tokyohost/pico-vision/monitor/assert/fishQr.png

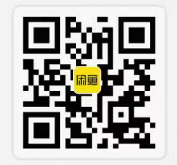
monitor/assert/fishQr.png
