tokyohost/pico-vision/monitor/assert/qqgroup.png

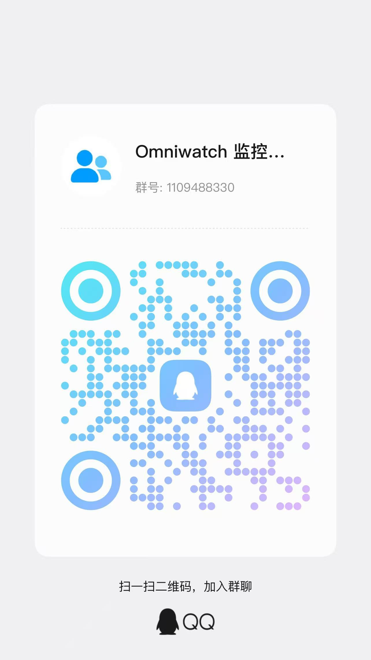
monitor/assert/qqgroup.png
