tokyohost/pico-vision/monitor/win/ui-web/assert/style/disk.png

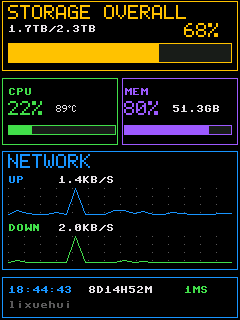
monitor/win/ui-web/assert/style/disk.png
