tokyohost/pico-vision/monitor/win/ui-web/assert/style/diskv2.png

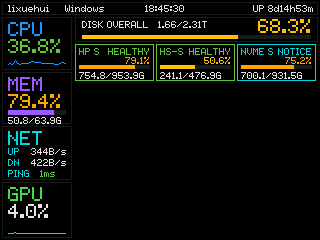
monitor/win/ui-web/assert/style/diskv2.png
