tokyohost/pico-vision/monitor/win/ui-web/assert/style/fps_simple.png

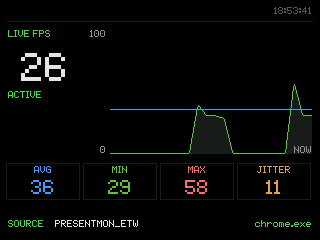
monitor/win/ui-web/assert/style/fps_simple.png
