tokyohost/pico-vision/monitor/win/ui-web/assert/style/game.png

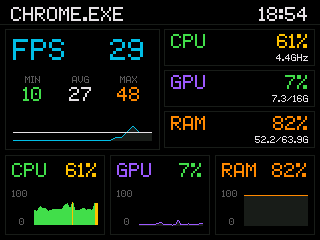
monitor/win/ui-web/assert/style/game.png
