tokyohost/pico-vision/monitor/win/ui-web/assert/style/horizontal_disk4x_qb.png

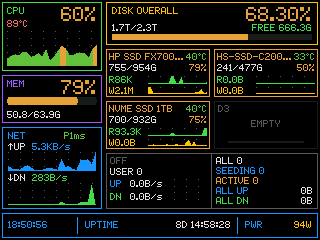
monitor/win/ui-web/assert/style/horizontal_disk4x_qb.png
