tokyohost/pico-vision/monitor/win/ui-web/assert/style/horizontal_disk.png

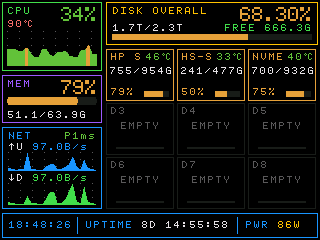
monitor/win/ui-web/assert/style/horizontal_disk.png
