tokyohost/pico-vision/monitor/win/ui-web/assert/style/horizontal_diskv2.png

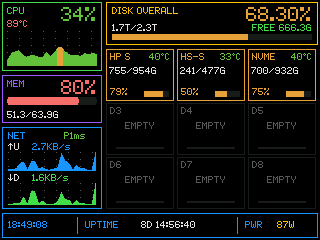
monitor/win/ui-web/assert/style/horizontal_diskv2.png
