tokyohost/pico-vision/monitor/win/ui-web/assert/style/simple.png

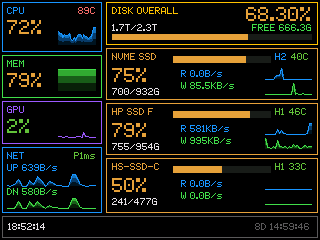
monitor/win/ui-web/assert/style/simple.png
