tokyohost/pico-vision/monitor/win/ui-web/assert/style/thermal_watch.png

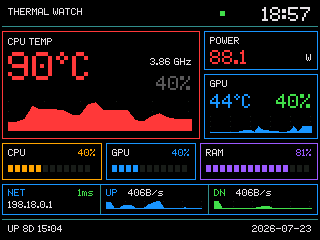
monitor/win/ui-web/assert/style/thermal_watch.png
