tokyohost/pico-vision/pcb/LED_MOSFET_PWM_V4_JLC_FREE_完整资料包/led_mosfet_pwm_board_v4_jlc_free/pcb_preview_v4_jlc_free.png

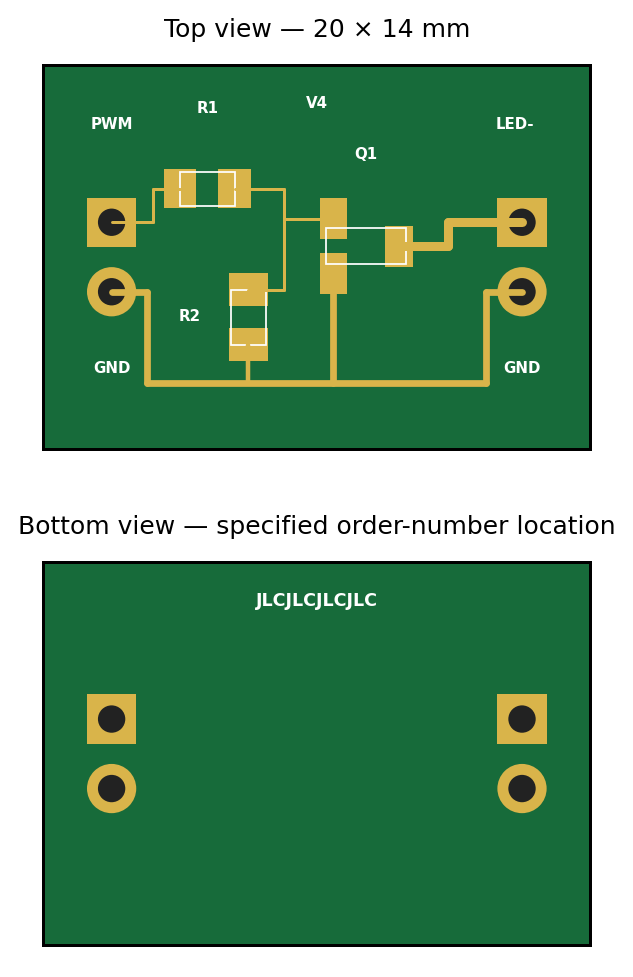
pcb/LED_MOSFET_PWM_V4_JLC_FREE_完整资料包/led_mosfet_pwm_board_v4_jlc_free/pcb_preview_v4_jlc_free.png
