tokyohost/pico-vision/pcb/v12/build/03_Docs/dimensions.png

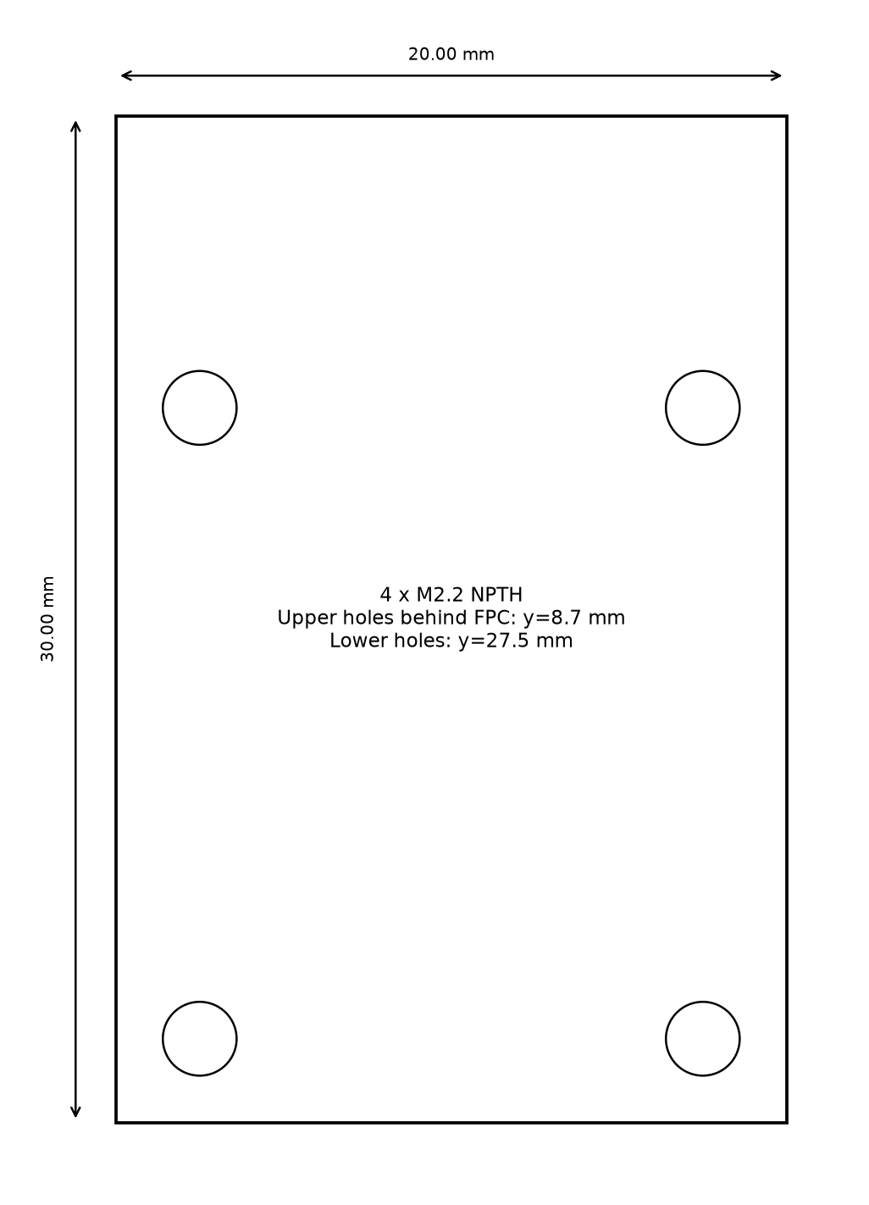
pcb/v12/build/03_Docs/dimensions.png
