tokyohost/pico-vision/pcb/v12/build/03_Docs/gerber_orientation_check.png

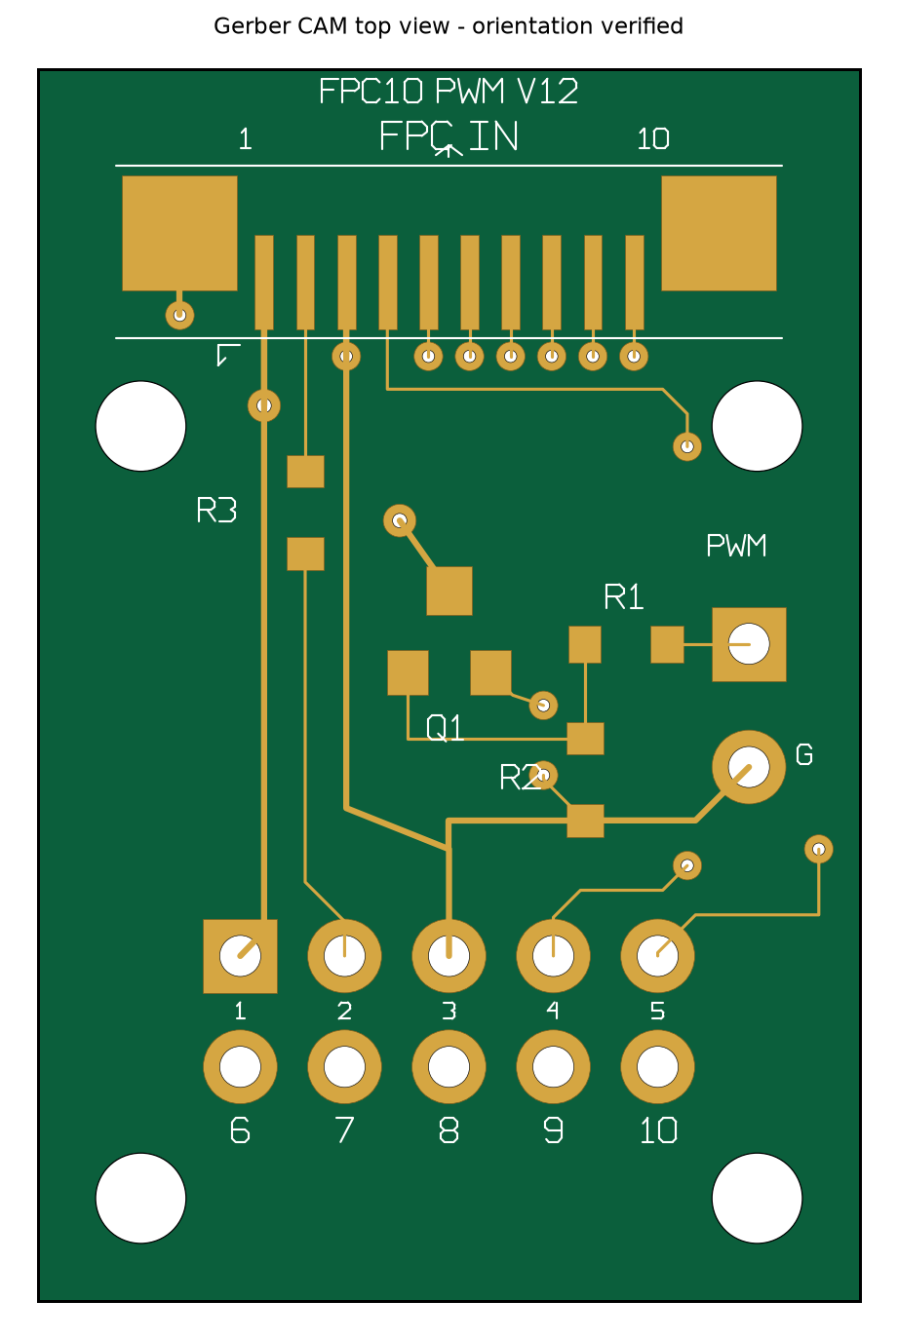
pcb/v12/build/03_Docs/gerber_orientation_check.png
