tokyohost/pico-vision/pcb/v12/build/03_Docs/preview_bottom.png

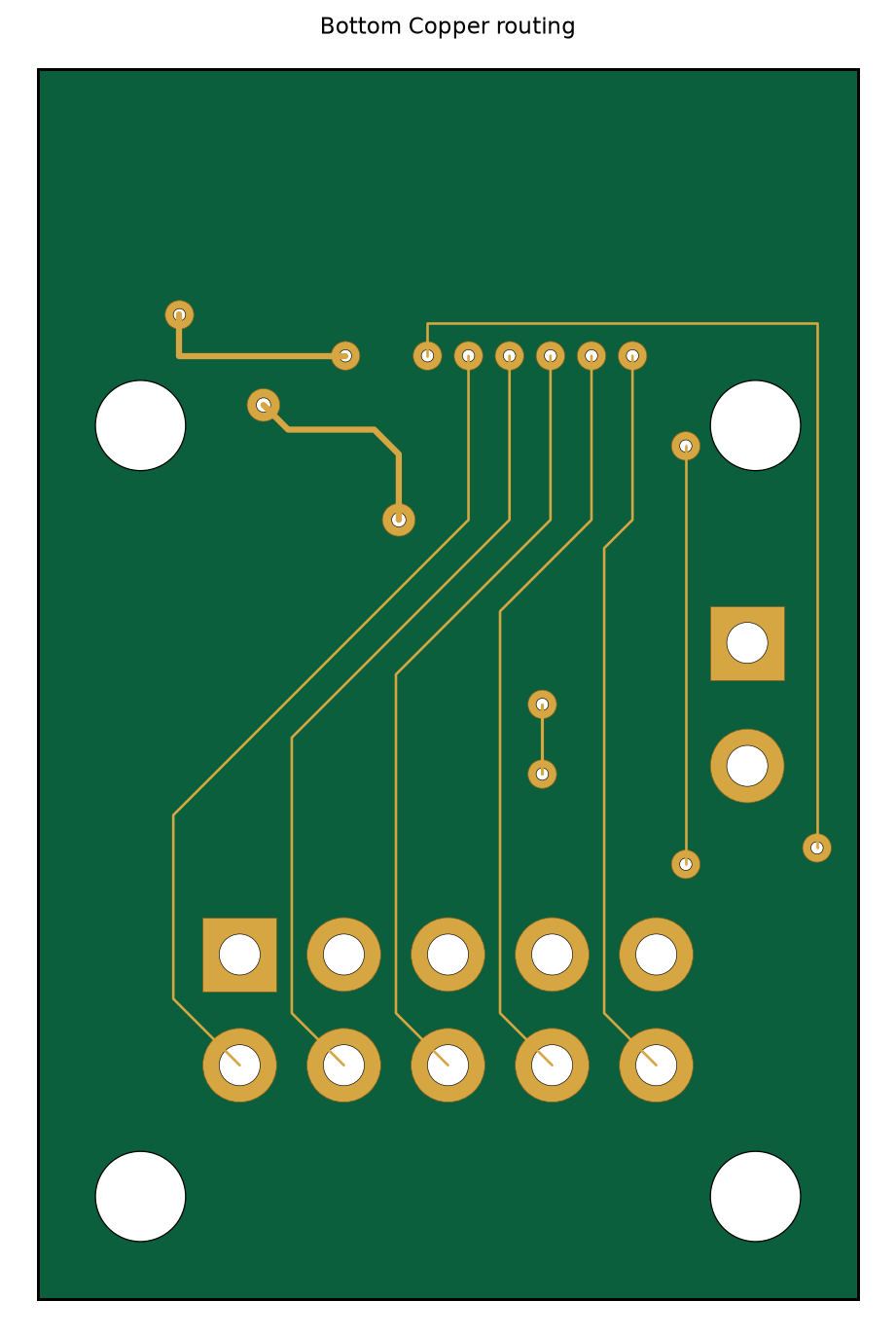
pcb/v12/build/03_Docs/preview_bottom.png
