tokyohost/pico-vision/monitor/custom_data_runner.py

#!/usr/bin/env python3
"""在隔离子进程中加载自定义数据插件并输出协议 JSON。"""

import importlib.util
import contextlib
import json
import sys
import traceback
from pathlib import Path


def _load_module(script_path):
    """从指定入口文件加载插件模块。"""
    plugin_directory = str(Path(script_path).resolve().parent)
    if plugin_directory not in sys.path:
        sys.path.insert(0, plugin_directory)
    specification = importlib.util.spec_from_file_location("omniwatch_custom_data_plugin", script_path)
    if specification is None or specification.loader is None:
        raise RuntimeError("无法加载插件入口模块")
    module = importlib.util.module_from_spec(specification)
    specification.loader.exec_module(module)
    return module


def _load_collect(script_path):
    """加载插件并返回经过校验的 collect 方法。"""
    with contextlib.redirect_stdout(sys.stderr):
        module = _load_module(script_path)
        collect = getattr(module, "collect", None)
        if not callable(collect):
            raise RuntimeError("插件入口必须定义 collect() 方法")
    return collect


def _collect(collect, config_json):
    """执行已加载的 collect 方法并校验返回值可序列化。"""
    with contextlib.redirect_stdout(sys.stderr):
        parameters = __import__("inspect").signature(collect).parameters
        result = collect() if not parameters else collect(config_json)
    json.dumps(result, ensure_ascii=False)
    return result


def main():
    """执行插件并仅向标准输出写入一条协议 JSON。"""
    if len(sys.argv) != 2:
        print(json.dumps({"ok": False, "error": "缺少插件入口路径"}, ensure_ascii=False))
        return 2
    try:
        collect = _load_collect(Path(sys.argv[1]).resolve())
    except Exception:
        print(json.dumps({"ok": False, "error": traceback.format_exc()}, ensure_ascii=False), flush=True)
        return 1
    for line in sys.stdin:
        try:
            request = json.loads(line)
            if request.get("command") == "stop":
                return 0
            if request.get("command") != "collect":
                raise RuntimeError("不支持的插件进程命令")
            response = {"ok": True, "data": _collect(collect, request.get("config", "{}"))}
        except Exception:
            response = {"ok": False, "error": traceback.format_exc()}
        print(json.dumps(response, ensure_ascii=False), flush=True)
    return 0


if __name__ == "__main__":
    raise SystemExit(main())
