tokyohost/pico-vision/monitor/monitor_core/style_commands.py

"""Pico 样式、截图与热配置命令处理。"""

import json
import logging
import os
import queue
from datetime import datetime
from pathlib import Path

import serial

from .console import configure_logging
from .ui_helpers import normalize_style_catalog

LOGGER = logging.getLogger("pico-monitor")
BUILTIN_LCD_STYLES = (
    "default", "disk", "diskv2", "diskv3", "diskv4", "horizontal_disk",
    "horizontal_diskv2", "horizontal_disk4x", "horizontal_disk4x_qb",
    "horizontal_disk6x", "simple", "fpstest", "fps_simple", "game",
    "idle",
)


class StyleCommandMixin:
    """提供样式管理、截图和运行时显示配置能力。"""

    def _synchronize_style_catalog(self):
        """接收 Pico 样式清单并更新 monitor 的 JSON 配置文件。"""
        catalog = getattr(self.client, "styles", None)
        if catalog is None:
            return
        catalog = catalog if isinstance(catalog, (list, tuple)) else []
        names = set(BUILTIN_LCD_STYLES)
        names.update({
            item.get("name") for item in catalog
            if isinstance(item, dict) and item.get("name")
        })
        if not names:
            return
        self.available_styles = names
        self.available_idle_styles = {
            item.get("name") for item in catalog
            if isinstance(item, dict) and item.get("name") and item.get("idle") is True
        } or {"idle"}
        settings_path = os.getenv("PICO_MONITOR_SETTINGS_PATH")
        if settings_path:
            from win.settings import TraySettingsStore

            normalized = normalize_style_catalog(catalog)
            if normalized:
                store = TraySettingsStore(settings_path)
                settings = store.load()
                settings["styles"] = normalized
                if settings["lcd_style"] not in names:
                    settings["lcd_style"] = normalized[0]["name"]
                    self.arguments.lcd_style = settings["lcd_style"]
                if settings["idle_style"] not in self.available_idle_styles:
                    settings["idle_style"] = "idle"
                    self.arguments.idle_style = settings["idle_style"]
                store.save(settings)
        LOGGER.info("STYLE_CATALOG_UPDATED：已同步 %d 个 Pico 样式", len(names))

    def request_reboot_and_stop(self):
        """让主循环退出，并在释放串口前请求 Pico 重启。"""
        LOGGER.info("收到托盘退出请求，将在停止监控前重启 Pico")
        self.reboot_requested.set()
        self.stopping.set()

    def request_sdk_bootloader_and_stop(self):
        """让主循环退出，并在释放 USB 前请求设备进入 ROM 下载模式。"""
        LOGGER.info("收到托盘 SDK 刷写请求，将在停止监控前切换 ROM USB 模式")
        self.sdk_bootloader_requested.set()
        self.stopping.set()

    def request_custom_style_catalog(self, result_queue=None):
        """安排主循环在当前串口交互结束后查询自定义样式。"""
        waiters = getattr(self, "custom_style_catalog_waiters", None)
        if result_queue is not None and waiters is not None:
            waiters.put(result_queue)
        self.custom_style_catalog_requested.set()

    def request_screenshot(self, result_queue=None):
        """安排主循环在当前串口交互完成后截取 LCD 画面。"""
        waiters = getattr(self, "screenshot_waiters", None)
        if result_queue is not None and waiters is not None:
            waiters.put(result_queue)
        self.screenshot_requested.set()

    def _publish_screenshot(self):
        """接收 Pico 截图、转换为 PNG，并把保存结果输出给托盘。"""
        self.screenshot_requested.clear()
        try:
            from PIL import Image

            metadata, pixels = self.client.screenshot()
            width = int(metadata["width"])
            height = int(metadata["height"])
            # Pillow 的 BGR;16 解码器读取小端 RGB565，Pico 回传的是 LCD 使用的
            # 大端字节序，因此先按像素交换高低字节再生成 PNG。
            little_endian_pixels = bytearray(len(pixels))
            little_endian_pixels[0::2] = pixels[1::2]
            little_endian_pixels[1::2] = pixels[0::2]
            image = Image.frombytes(
                "RGB", (width, height), bytes(little_endian_pixels), "raw", "BGR;16"
            )
            screenshot_directory = Path(
                os.getenv("PICO_MONITOR_SCREENSHOT_DIR", Path.cwd() / "screenshot")
            )
            screenshot_directory.mkdir(parents=True, exist_ok=True)
            path = screenshot_directory / datetime.now().strftime(
                "screenshot_%Y%m%d_%H%M%S_%f.png"
            )
            image.save(path, "PNG")
            result = {"status": "ok", "path": str(path.resolve())}
        except (KeyError, OSError, RuntimeError, ValueError, serial.SerialException) as error:
            result = {"status": "error", "message": str(error)}
        print(
            "SCREENSHOT_RESULT:"
            + json.dumps(result, ensure_ascii=False, separators=(",", ":")),
            flush=True,
        )
        waiters = getattr(self, "screenshot_waiters", None)
        try:
            waiter = waiters.get_nowait() if waiters is not None else None
        except queue.Empty:
            waiter = None
        if waiter is not None:
            waiter.put(result)

    def _publish_custom_style_catalog(self):
        """通过 Pico 指令查询全部样式，同步配置后输出给托盘进程。"""
        self.custom_style_catalog_requested.clear()
        try:
            catalog = self.client.request_style_catalog_info()
            latest_styles = catalog["styles"]
            if not isinstance(latest_styles, list):
                raise ValueError("设备样式目录格式无效")
            self.client.styles = latest_styles
            self._synchronize_style_catalog()
            result = {
                "status": "ok",
                "styles": latest_styles,
                "flash": catalog["flash"],
                "active_style": catalog.get("active_style", ""),
            }
        except (KeyError, ValueError, OSError, RuntimeError, serial.SerialException) as error:
            result = {"status": "error", "message": str(error), "styles": []}
        print(
            "CUSTOM_STYLE_LIST_RESULT:"
            + json.dumps(result, ensure_ascii=False, separators=(",", ":")),
            flush=True,
        )
        waiters = getattr(self, "custom_style_catalog_waiters", None)
        try:
            waiter = waiters.get_nowait() if waiters is not None else None
        except queue.Empty:
            waiter = None
        if waiter is not None:
            waiter.put(result)

    def request_custom_style_upload(self, payload, result_queue=None):
        """安排主循环在串口空闲时上传一个已校验的自定义样式。"""
        waiters = getattr(self, "custom_style_upload_waiters", None)
        if result_queue is not None and waiters is not None:
            waiters.put(result_queue)
        self.custom_style_uploads.put(dict(payload))

    def _publish_custom_style_upload(self):
        """执行待处理的自定义样式上传并向托盘输出结构化结果。"""
        payload = self.custom_style_uploads.get_nowait()
        try:
            import base64

            content = base64.b64decode(payload["content"], validate=True)

            def publish_progress(progress):
                """输出样式上传进度，供管理界面实时展示已发送字节数。"""
                print(
                    "CUSTOM_STYLE_UPLOAD_PROGRESS:"
                    + json.dumps(
                        progress,
                        ensure_ascii=False,
                        separators=(",", ":"),
                    ),
                    flush=True,
                )

            data = self.client.upload_style(
                payload["filename"],
                payload["style_name"],
                content,
                overwrite=payload.get("overwrite") is True,
                progress_callback=publish_progress,
            )
            result = {"status": "ok", "data": data}
            self.client.styles = self.client.request_style_catalog()
            self._synchronize_style_catalog()
        except (KeyError, ValueError, OSError, RuntimeError, serial.SerialException) as error:
            result = {"status": "error", "message": str(error)}
        print(
            "CUSTOM_STYLE_UPLOAD_RESULT:"
            + json.dumps(result, ensure_ascii=False, separators=(",", ":")),
            flush=True,
        )
        waiters = getattr(self, "custom_style_upload_waiters", None)
        try:
            waiter = waiters.get_nowait() if waiters is not None else None
        except queue.Empty:
            waiter = None
        if waiter is not None:
            waiter.put(result)

    def request_custom_style_delete(self, payload, result_queue=None):
        """安排主循环删除指定自定义样式。"""
        waiters = getattr(self, "custom_style_delete_waiters", None)
        if result_queue is not None and waiters is not None:
            waiters.put(result_queue)
        self.custom_style_deletes.put(dict(payload))

    def _publish_custom_style_delete(self):
        """删除设备自定义样式、刷新目录并向托盘发布结果。"""
        payload = self.custom_style_deletes.get_nowait()
        try:
            data = self.client.delete_style(
                payload["filename"], payload["style_name"],
            )
            latest_styles = data.get("styles")
            if not isinstance(latest_styles, list):
                raise ValueError("设备删除响应缺少最新样式列表")
            self.client.styles = latest_styles
            self._synchronize_style_catalog()
            result = {
                "status": "ok",
                "data": data,
                "styles": latest_styles,
            }
        except (KeyError, ValueError, OSError, RuntimeError, serial.SerialException) as error:
            result = {"status": "error", "message": str(error)}
        print(
            "CUSTOM_STYLE_DELETE_RESULT:"
            + json.dumps(result, ensure_ascii=False, separators=(",", ":")),
            flush=True,
        )
        waiters = getattr(self, "custom_style_delete_waiters", None)
        try:
            waiter = waiters.get_nowait() if waiters is not None else None
        except queue.Empty:
            waiter = None
        if waiter is not None:
            waiter.put(result)

    def apply_display_config(self, payload):
        """校验并热更新 Windows 托盘下发的显示配置。"""
        brightness = int(payload.get("lcd_brightness", self.arguments.lcd_brightness))
        rotation = int(payload.get("screen_rotation", self.arguments.screen_rotation))
        style = payload.get("lcd_style", self.arguments.lcd_style)
        idle_enabled = bool(payload.get("idle_enabled", getattr(self.arguments, "idle_enabled", True)))
        idle_style = payload.get("idle_style", getattr(self.arguments, "idle_style", "idle"))
        idle_timeout = int(payload.get("idle_timeout", getattr(self.arguments, "idle_timeout", 30)))
        network_unit = payload.get("network_unit", self.arguments.network_unit)
        if not 1 <= brightness <= 100:
            raise ValueError("LCD 背光亮度必须为 1 至 100")
        if rotation not in (0, 180):
            raise ValueError("屏幕旋转角度仅支持 0 或 180")
        if style not in self.available_styles:
            raise ValueError("不支持的 LCD 样式")
        if idle_enabled and idle_style not in getattr(self, "available_idle_styles", {"idle"}):
            raise ValueError("不支持的 LCD 待机样式")
        if idle_enabled and idle_timeout <= 0:
            raise ValueError("待机秒数必须大于 0")
        if network_unit not in ("MB", "Mbps"):
            raise ValueError("不支持的网络速率单位")
        self.arguments.lcd_brightness = brightness
        self.arguments.screen_rotation = rotation
        self.arguments.lcd_style = style
        self.arguments.idle_enabled = idle_enabled
        self.arguments.idle_style = idle_style
        self.arguments.idle_timeout = idle_timeout
        self.arguments.network_unit = network_unit
        LOGGER.info(
            "显示设置已热更新：亮度=%d%%，旋转=%d°，样式=%s，允许待机=%s，待机样式=%s，待机=%d 秒，网络单位=%s",
            brightness, rotation, style, idle_enabled, idle_style, idle_timeout, network_unit,
        )

    def apply_dev_config(self, payload):
        """热更新开发模式开关，不重启 Monitor 工作进程。"""
        enabled = payload.get("enabled")
        if not isinstance(enabled, bool):
            raise ValueError("开发模式开关必须为布尔值")
        self.arguments.dev = enabled
        configure_logging("DEBUG" if enabled else self.arguments.log_level)
        LOGGER.info("开发模式已热更新：%s", "开启" if enabled else "关闭")

    def stop(self, signum=None, frame=None):
        """请求主循环停止，由通信线程在退出阶段统一关闭串口。"""
        del signum, frame
        LOGGER.info("收到停止请求，正在关闭监控程序")
        # Windows 的 PySerial 正在 ReadFile 时不能由其他线程执行 close，
        # 否则内部 OVERLAPPED 事件会被置空并触发 ctypes.byref(None) 异常。
        self.stopping.set()
