tokyohost/pico-vision/monitor/sdk_flash.py

"""校验 ESP32-S3 SDK 镜像并通过 esptool 执行受控 USB 刷写。"""

import argparse
import hashlib
import json
import re
import struct
import sys
import time
from contextlib import redirect_stdout
from dataclasses import dataclass
from pathlib import Path

from serial.tools import list_ports


ESP32_IMAGE_MAGIC = 0xE9
ESP32_S3_IMAGE_CHIP_ID = 9
ESP32_S3_PARTITION_TABLE_OFFSET = 0x8000
ESP32_S3_APPLICATION_OFFSET = 0x10000
ESPRESSIF_USB_VENDOR_ID = 0x303A
PARTITION_ENTRY_MAGIC = 0x50AA
PARTITION_ENTRY_SIZE = 32
MAXIMUM_SDK_IMAGE_SIZE = 8 * 1024 * 1024
SDK_VERSION_PATTERN = re.compile(
    rb"MPY version\s*:\s*(v[^\x00\r\n]{1,80}?)\s+on\s+\d{4}-\d{2}-\d{2}"
)


@dataclass(frozen=True)
class SdkPartition:
    """保存 SDK 合并镜像中的一个 ESP32 分区表项。"""

    partition_type: int
    subtype: int
    offset: int
    size: int
    label: str


@dataclass(frozen=True)
class SdkImageInformation:
    """保存通过全部安全校验的 SDK 镜像摘要。"""

    path: Path
    size: int
    sha256: str
    sdk_version: str
    partitions: tuple


class _ForwardingTextRecorder:
    """实时转发 esptool 标准输出，并保留用于判断收尾状态的文本。"""

    def __init__(self, target):
        """保存输出目标并初始化本次刷写的文本片段。"""
        self._target = target
        self._parts = []

    def write(self, content):
        """记录并立即转发一段文本，保持界面刷写日志实时更新。"""
        text = str(content)
        self._parts.append(text)
        return self._target.write(text)

    def flush(self):
        """立即刷新真实输出目标。"""
        return self._target.flush()

    def isatty(self):
        """返回真实输出目标的终端能力。"""
        method = getattr(self._target, "isatty", None)
        return bool(method()) if method is not None else False

    def getvalue(self):
        """合并并返回已经记录的全部输出。"""
        return "".join(self._parts)

    def __getattr__(self, name):
        """把编码等其他文本流属性转发给真实输出目标。"""
        return getattr(self._target, name)


def _is_verified_watchdog_reset_disconnect(error, output):
    """判断异常是否仅由校验成功后的 watchdog 复位移除串口引起。"""
    normalized_output = str(output).lower()
    if (
        "hash of data verified" not in normalized_output
        or "hard resetting with a watchdog" not in normalized_output
    ):
        return False

    normalized_error = str(error).lower()
    device_missing = (
        getattr(error, "winerror", None) == 433
        or "指定不存在的设备" in normalized_error
        or "winerror 433" in normalized_error
        or "none, 433" in normalized_error
        or "device does not exist" in normalized_error
    )
    return device_missing and "cannot configure port" in normalized_error
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
